andyofmars/gp-shield/Hardware/Electrical/Sim/5v-reg.asc

C1: cap; 10µ
C2: cap; 10µ
R1: res
R2: res
R3: res
R4: res
R5: res
U1: ncp1117_50-x
Vcc: voltage; 12
Vripple: voltage; SINE(0 0.1 1K)
Named nets: 0
