andyofmars/gp-shield/Hardware/Electrical/Sim/power-supply.asc

D1: zener; TDZ6_2B
D2: schottky
D3: zener; BZX84C22VL
M1: pmos; IRF7404
R1: res; 0.01
R2: res; 10R
R3: res; 10k
R4: res; 10K
R5: res; 22k
R6: res; 5.6k
R7: res; 7k
R8: res; 3k
R9: res; 1K
R10: res; 40K
S1: sw; MYSW
U1: LT1389-2.5
U2: LT1017
Vbatt1: voltage; 5
Vbatt: voltage; 12
Named nets: 0
.dc Vbatt -10 30
Fuse
OCP
Reverse
Polarity
Protection
OVP (22V)
Adjustable UVLO
(10K trim-pot for 6V-17V)
with Hysteresis (10% at 10V)
High side Switch
.model MYSW SW(Ron=1 Roff=1Meg Vt=.5 Vh=0)
Power switch
(modelled as voltage controlled switch
to analyse transients)
Load
